46nori/GlimmerGo/doc/images/DevEnvironment1.png

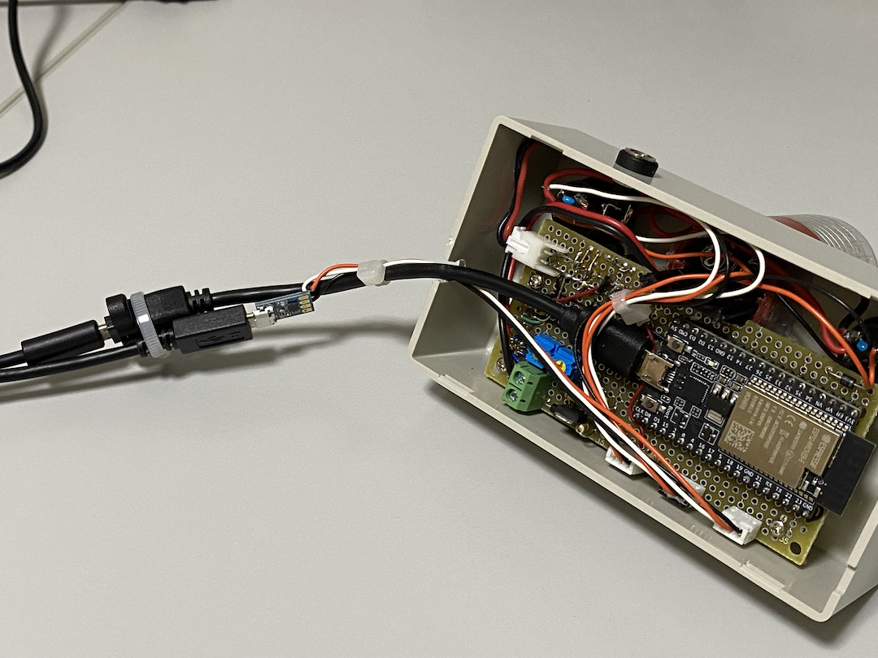
doc/images/DevEnvironment1.png
