46nori/GlimmerGo/doc/images/DevEnvironment2.png

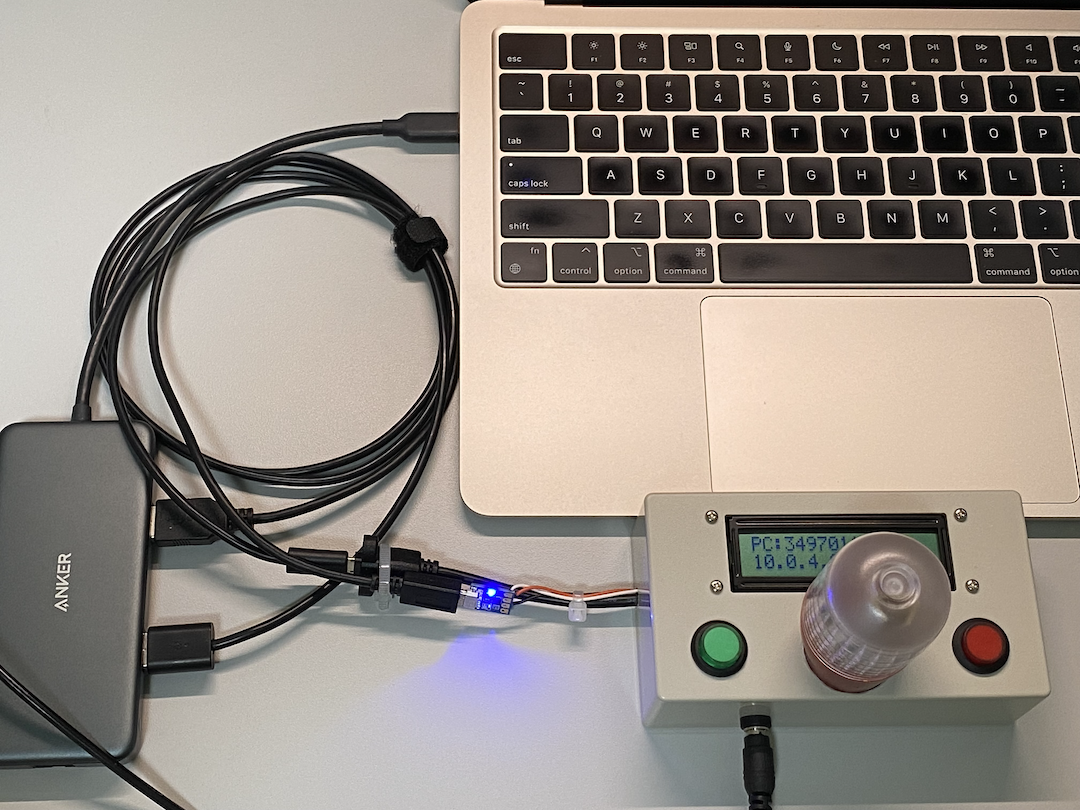
doc/images/DevEnvironment2.png
