46nori/GlimmerGo/KiCad/GlimmerGo/GlimmerGo.kicad_sch

## KiCad design KiCad/GlimmerGo/GlimmerGo.kicad_sch (2024-08-06)

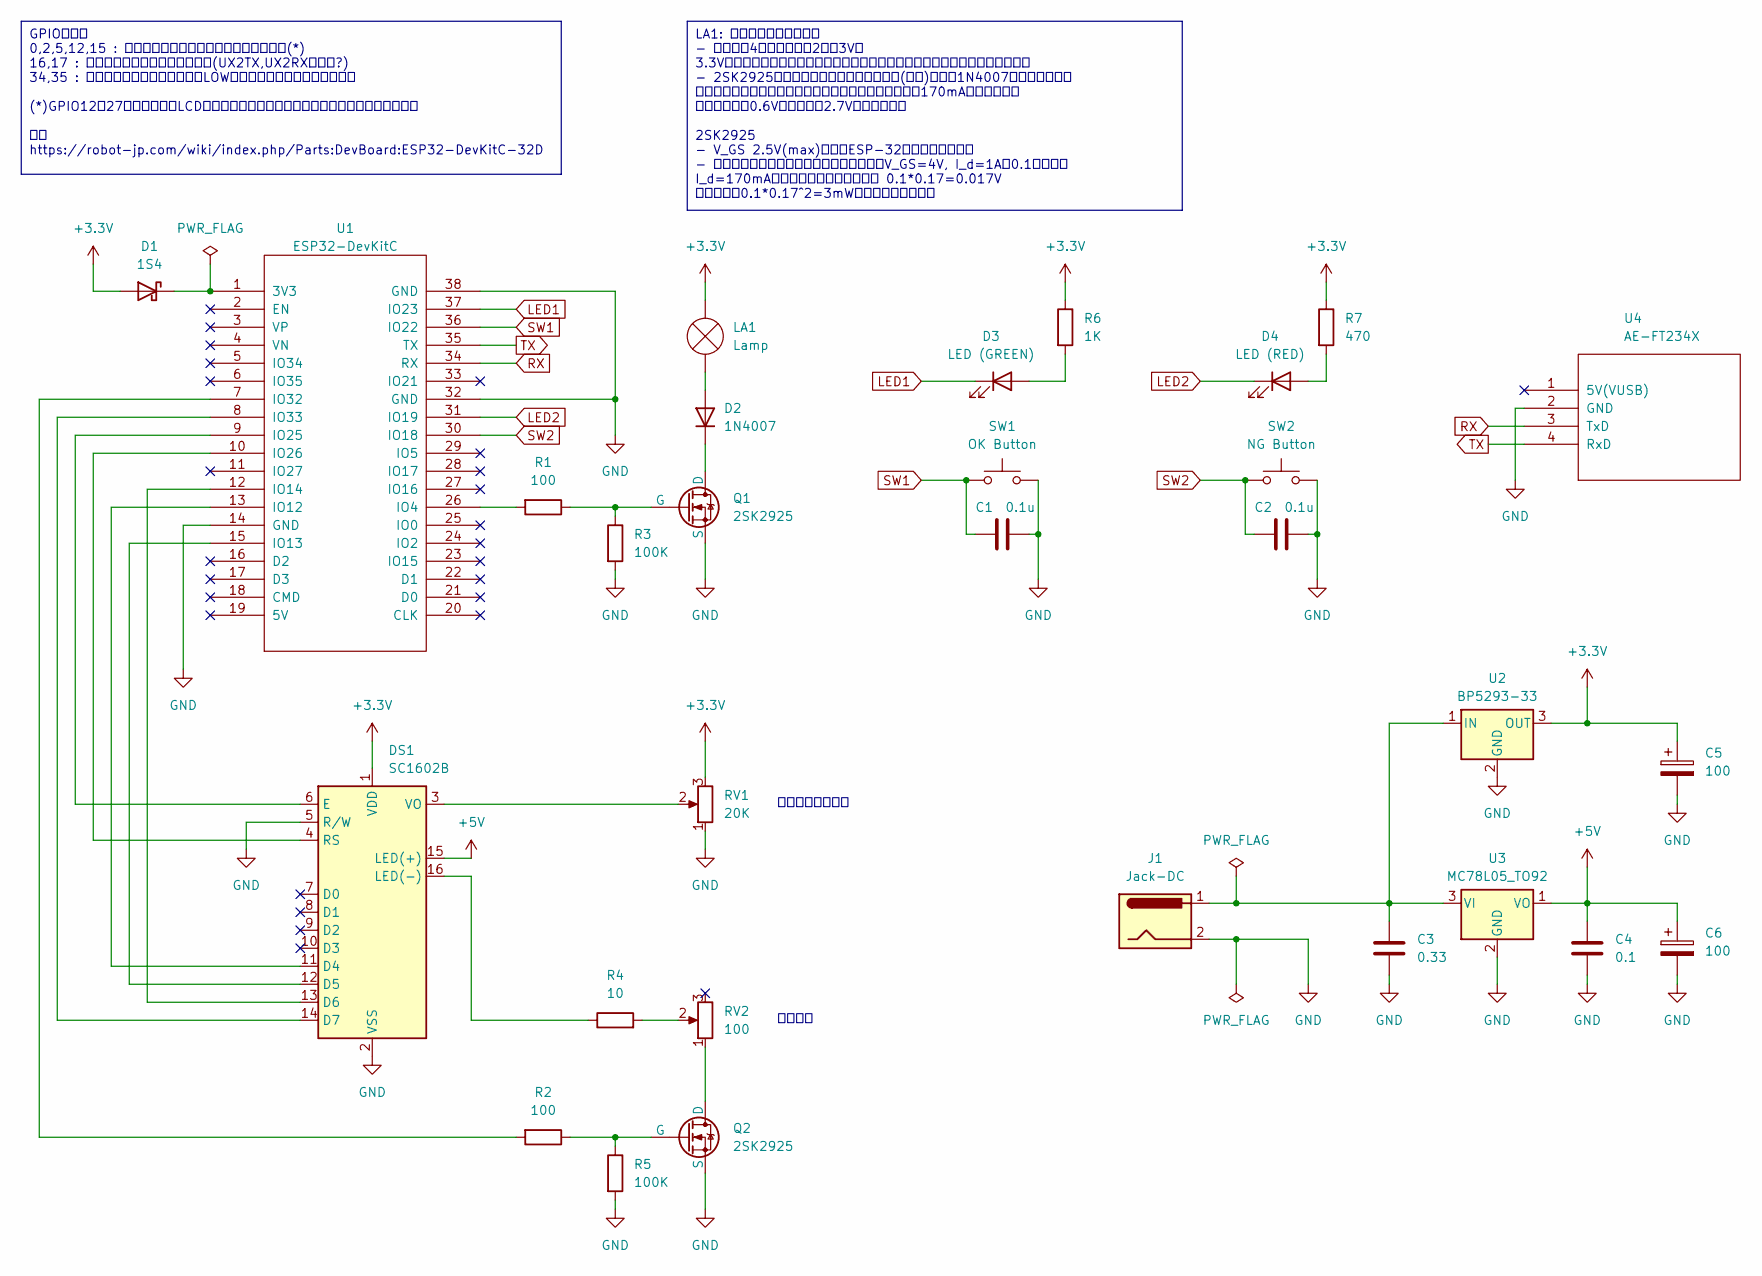
[picture p38: schematic GlimmerGo.kicad_sch]

Parts:
C1, C2: 0.1u
C3: 0.33
C4: 0.1
C5, C6: 100
D1: 1S4; D_DO-41_SOD81_P10.16mm_Horizontal
D2: 1N4007
D3: LED (GREEN)
D4: LED (RED)
DS1: SC1602B
J1: Jack-DC
LA1: Lamp
Q1, Q2: 2SK2925
R1, R2: 100
R3, R5: 100K
R4: 10
R6: 1K
R7: 470
RV1: 20K
RV2: 100
SW1: OK Button
SW2: NG Button
U1: ESP32-DevKitC; MODULE
U2: BP5293-33; TO-220-3_Vertical
U3: MC78L05_TO92; TO-92_Inline
U4: AE-FT234X; MODULE

Connections:
+3.3V: C5.1, D1.2 (A), DS1.1 (VDD), LA1.2 (+), R6.1, R7.1, RV1.3, U2.3 (OUT)
+5V: C4.1, C6.1, DS1.15 (LED(+)), U3.1 (VO)
GND: C1.1, C2.1, C3.2, C4.2, C5.2, C6.2, DS1.2 (VSS), DS1.5 (R/W), J1.2, Q1.3 (S), Q2.3 (S), R3.2, R5.2, RV1.1, SW1.2, SW2.2, U1.14 (GND), U1.32 (GND), U1.38 (GND), U2.2 (GND), U3.2 (GND), U4.2 (GND)
LED1: D3.1 (K), U1.37 (IO23)
LED2: D4.1 (K), U1.31 (IO19)
unnamed: C3.1, J1.1, U2.1 (IN), U3.3 (VI)
unnamed: D1.1 (K), U1.1 (3V3)
unnamed: D2.1 (K), Q1.1 (D)
unnamed: D2.2 (A), LA1.1 (-)
unnamed: D3.2 (A), R6.2
unnamed: D4.2 (A), R7.2
unnamed: DS1.3 (VO), RV1.2
unnamed: DS1.4 (RS), U1.10 (IO26)
unnamed: DS1.6 (E), U1.9 (IO25)
unnamed: DS1.11 (D4), U1.13 (IO12)
unnamed: DS1.12 (D5), U1.15 (IO13)
unnamed: DS1.13 (D6), U1.12 (IO14)
unnamed: DS1.14 (D7), U1.8 (IO33)
unnamed: DS1.16 (LED(-)), R4.1
unnamed: Q1.2 (G), R1.1, R3.1
unnamed: Q2.1 (D), RV2.1
unnamed: Q2.2 (G), R2.1, R5.1
unnamed: R1.2, U1.26 (IO4)
unnamed: R2.2, U1.7 (IO32)
unnamed: R4.2, RV2.2
RX: U1.34 (RX), U4.3 (TxD)
SW1: C1.2, SW1.1, U1.36 (IO22)
SW2: C2.2, SW2.1, U1.30 (IO18)
TX: U1.35 (TX), U4.4 (RxD)

Notes on the sheet:
LA1: エーモン 非常信号灯 - 電源は単4アルカリ電池2本で3V。 3.3Vを供給すると点滅周期が速くなり制御回路にダメージを与える恐れがある。 - 2SK2925のドレインソース間電圧は低い(後述)ので、1N4007の順方向電圧を 利用して電源電圧を下げている。点灯時の電流は実測で170mA程度なので、 電圧降下は約0.6V。よって約2.7Vで駆動する。 2SK2925 - V_GS 2.5V(max)なのでESP-32でドライブ可能。 - データシートよりドレインソース抵抗は、V_GS=4V, I_d=1Aで0.1オーム。 I_d=170mAではドレインソース電圧は 0.1*0.17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
GPIOの制約 0,2,5,12,15 : 起動モードに影響するので使用を避ける(*) 16,17 : 理由不明だが使用できなかった(UX2TX,UX2RXと衝突?) 34,35 : 入力専用で使えるはずだが、LOWに張り付いて使用できなかった (*)GPIO12を27に接続したがLCD駆動がうまくいかなかったのでそのままにしている。 参考 https://robot-jp.com/wiki/index.php/Parts:DevBoard:ESP32-DevKitC-32D
コントラスト調整
輝度調整
